Hoferlukaslh/M7-Lecteur-RFID/Images/Hardware/bornier.jpg

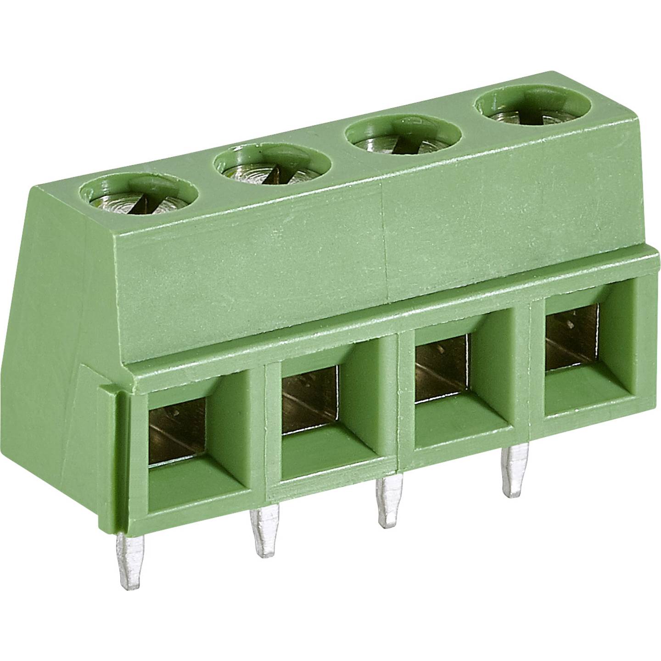
Images/Hardware/bornier.jpg
