Hoferlukaslh/M7-Lecteur-RFID/Images/Hardware/LED_SMD.jpeg

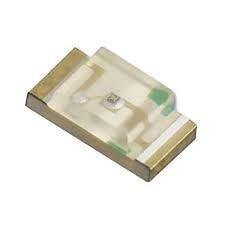
Images/Hardware/LED_SMD.jpeg
