Hoferlukaslh/M7-Lecteur-RFID/Images/Hardware/MAX3485.jpg

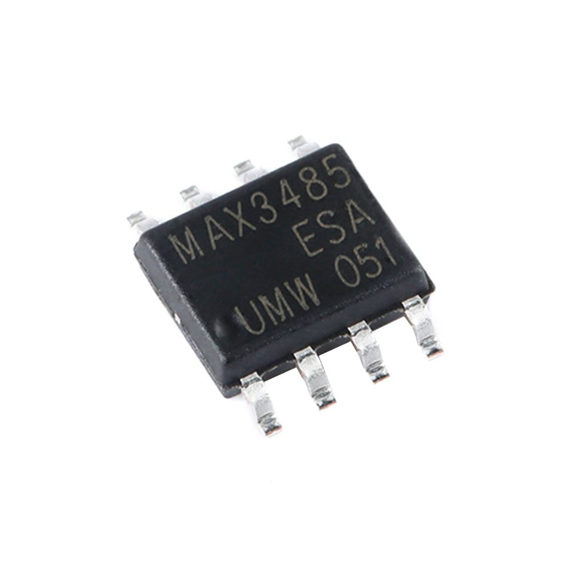
Images/Hardware/MAX3485.jpg
