Hoferlukaslh/M7-Lecteur-RFID/Images/Hardware/RS-485.jpeg

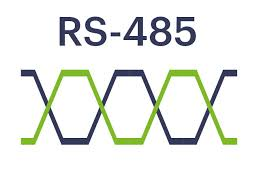
Images/Hardware/RS-485.jpeg
